meadowstress/Arduino_Watering_System/src/mock/mock_arduino.cpp

#include <sys/timeb.h>
#include "mock_arduino.h"
#include <iostream>
#include <ctime>
#include "parameter.h"

using namespace std;

// artificial states for actuators
bool pump_state         = false;
bool valve_state_top    = false;
bool valve_state_bottom = false;
bool valve_state_tube   = false;
bool switch_state       = true;
bool water_state        = false;
bool water_level_state  = false;
bool led_state          = false;
float temperature_value = 20;

// artificial local time
RTCDateTime current_local_time{2020, 04, 06, 11, 30, 00};

/*
This definition of HIGH and LOW is very volatile and is only valid for
switches connected to pulldown resistors. Currently there are 3 switches
implemented in the code.
*/

const bool HIGH = false;
const bool LOW  = true;

Output Serial;
DHT dht;

timeb t_start;

unsigned long millis()
{
    timeb t_now;
    ftime(&t_now);
    unsigned long ms =
        (t_now.time - t_start.time) * 1000 + (t_now.millitm - t_start.millitm);
    ms = ms * 100000;  // simulate time faster
    // return (t_now.time  - t_start.time) * 1000 + (t_now.millitm -
    // t_start.millitm);
    return (ms);
}

void digitalWrite(const short& pin, const bool& state)
{
    if (pin == par::PUMP)
    {
        if (state == HIGH)
            pump_state = false;
        else if (state == LOW)
            pump_state = true;
        else
            std::cout << "Throw Error: digitalWrite(PUMP)\n";
    }

    else if (pin == par::VALVETOP)
    {
        if (state == HIGH)
            valve_state_top = false;
        else if (state == LOW)
            valve_state_top = true;
        else
            std::cout << "Throw Error: digitalWrite(VALVETOP)\n";
    }

    else if (pin == par::VALVEBOTTOM)
    {
        if (state == HIGH)
            valve_state_bottom = false;
        else if (state == LOW)
            valve_state_bottom = true;
        else
            std::cout << "Throw Error: digitalWrite(VALVEBOTTOM)\n";
    }

    else if (pin == par::VALVETUBE)
    {
        if (state == HIGH)
            valve_state_tube = false;
        else if (state == LOW)
            valve_state_tube = true;
        else
            std::cout << "Throw Error: digitalWrite(VALVETUBE)\n";
    }

    else if (pin == par::WATERLEVEL)
    {
        if (state == HIGH)
            water_level_state = false;
        else if (state == LOW)
            water_level_state = true;
        else
            std::cout << "Throw Error: digitalWrite(WATERLEVEL)\n";
    }
    else if (pin == par::LED)
    {
        if (state == HIGH)
            led_state = false;
        else if (state == LOW)
            led_state = true;
        else
            std::cout << "Throw Error: digitalWrite(LED)\n";
    }
}

bool digitalRead(const short& pin)
{
    if (pin == par::PUMP)
        return (pump_state);

    else if (pin == par::VALVETOP)
        return (valve_state_top);

    else if (pin == par::VALVEBOTTOM)
        return (valve_state_bottom);

    else if (pin == par::SWITCH)
        return (switch_state);

    else if (pin == par::WATER)
        return (water_state);

    else if (pin == par::WATERLEVEL)
        return (water_level_state);

    else if (pin == par::VALVETUBE)
        return (valve_state_tube);

    else if (pin == par::LED)
        return (led_state);

    else
    {
        cout << "Throw Error: digitalRead \n";
        return HIGH;
    }
}

void Output::print(string data)
{
    cout << data;
}

void Output::println(string data)
{
    cout << data << endl;
}

void Output::print(long data)
{
    cout << data;
}

void Output::println(long data)
{
    cout << data << endl;
}

void Output::print(unsigned long data)
{
    cout << data;
}

void Output::println(unsigned long data)
{
    cout << data << endl;
}

void Output::print(unsigned int data)
{
    cout << data;
}

void Output::println(unsigned int data)
{
    cout << data << endl;
}

void Output::print(short data)
{
    cout << data;
}

void Output::println(short data)
{
    cout << data << endl;
}

void Output::print(float data)
{
    cout << data;
}

void Output::println(float data)
{
    cout << data << endl;
}

float DHT::readTemperature()
{
    return (temperature_value);
}

void DS3231::setDateTime(unsigned int iYear,
                         unsigned int iMonth,
                         unsigned int iDay,
                         unsigned int iHour,
                         unsigned int iMinute,
                         unsigned int iSecond)
{
    current_local_time.year   = iYear;
    current_local_time.month  = iMonth;
    current_local_time.day    = iDay;
    current_local_time.hour   = iHour;
    current_local_time.minute = iMinute;
    current_local_time.second = iSecond;
}

RTCDateTime DS3231::getDateTime()
{

    //  mocking with computer system time
    // time_t current_time_epoch = time(0);
    // tm *current_local_time = localtime(&current_time_epoch);

    RTCDateTime t;

    // set return value
    t.year   = current_local_time.year;
    t.month  = current_local_time.month;
    t.day    = current_local_time.day;
    t.hour   = current_local_time.hour;
    t.minute = current_local_time.minute;
    t.second = current_local_time.second;

    return t;
}

// mock SD Card variable
sd SD;
unsigned short FILE_WRITE = 1;

String F(String const input)
{
    return input;
}
